Eumel247/PhotoBooth/PiImage/layout/layout1.png

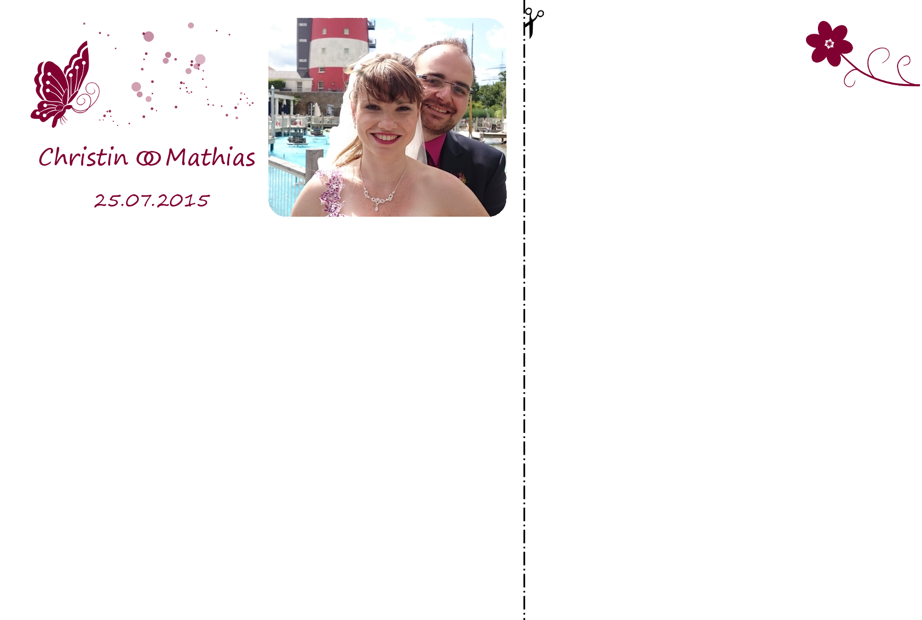
PiImage/layout/layout1.png
